rocketblaster/Devboard/attachments/3d_render.png

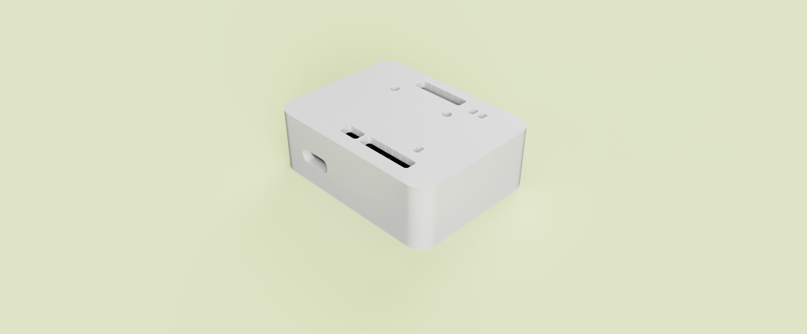
attachments/3d_render.png
