rocketblaster/Devboard/attachments/image3.png

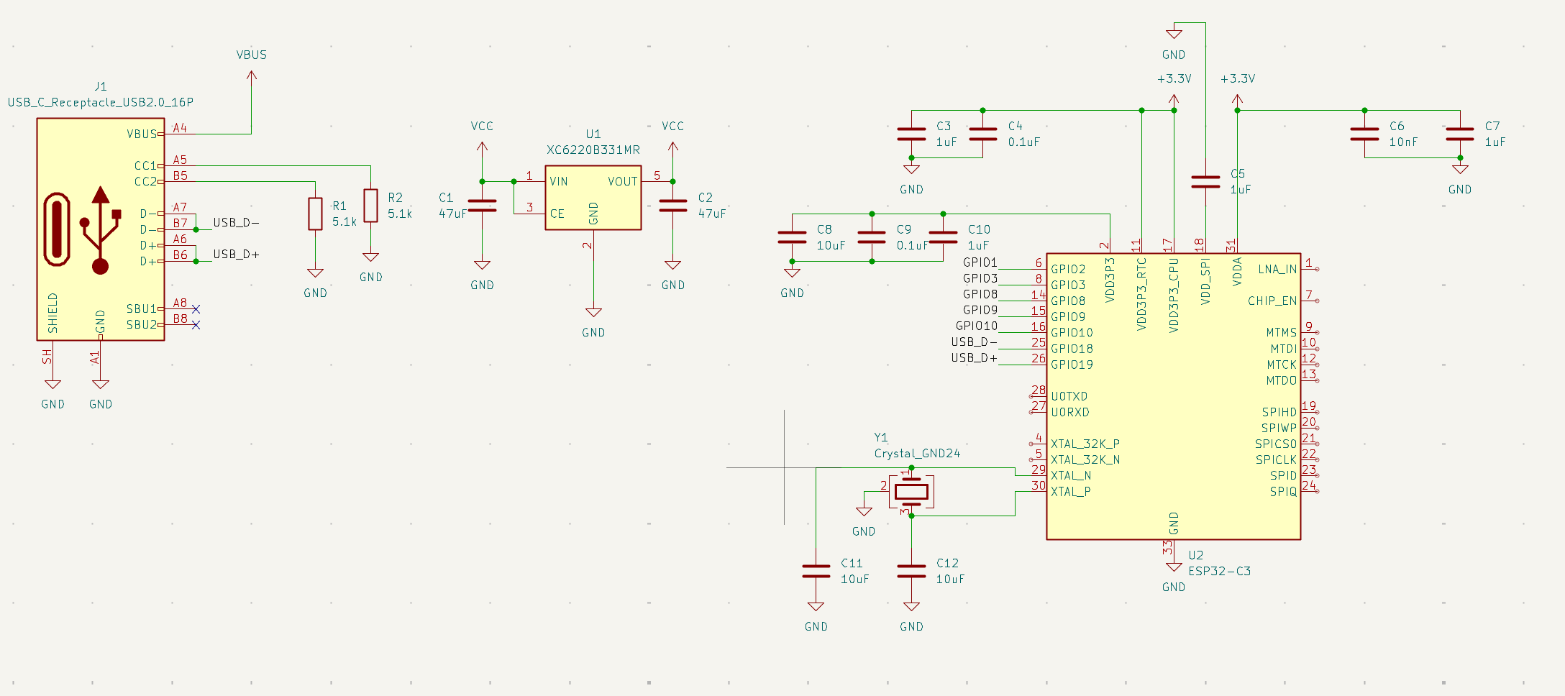
attachments/image3.png
