rocketblaster/Devboard/attachments/image12.png

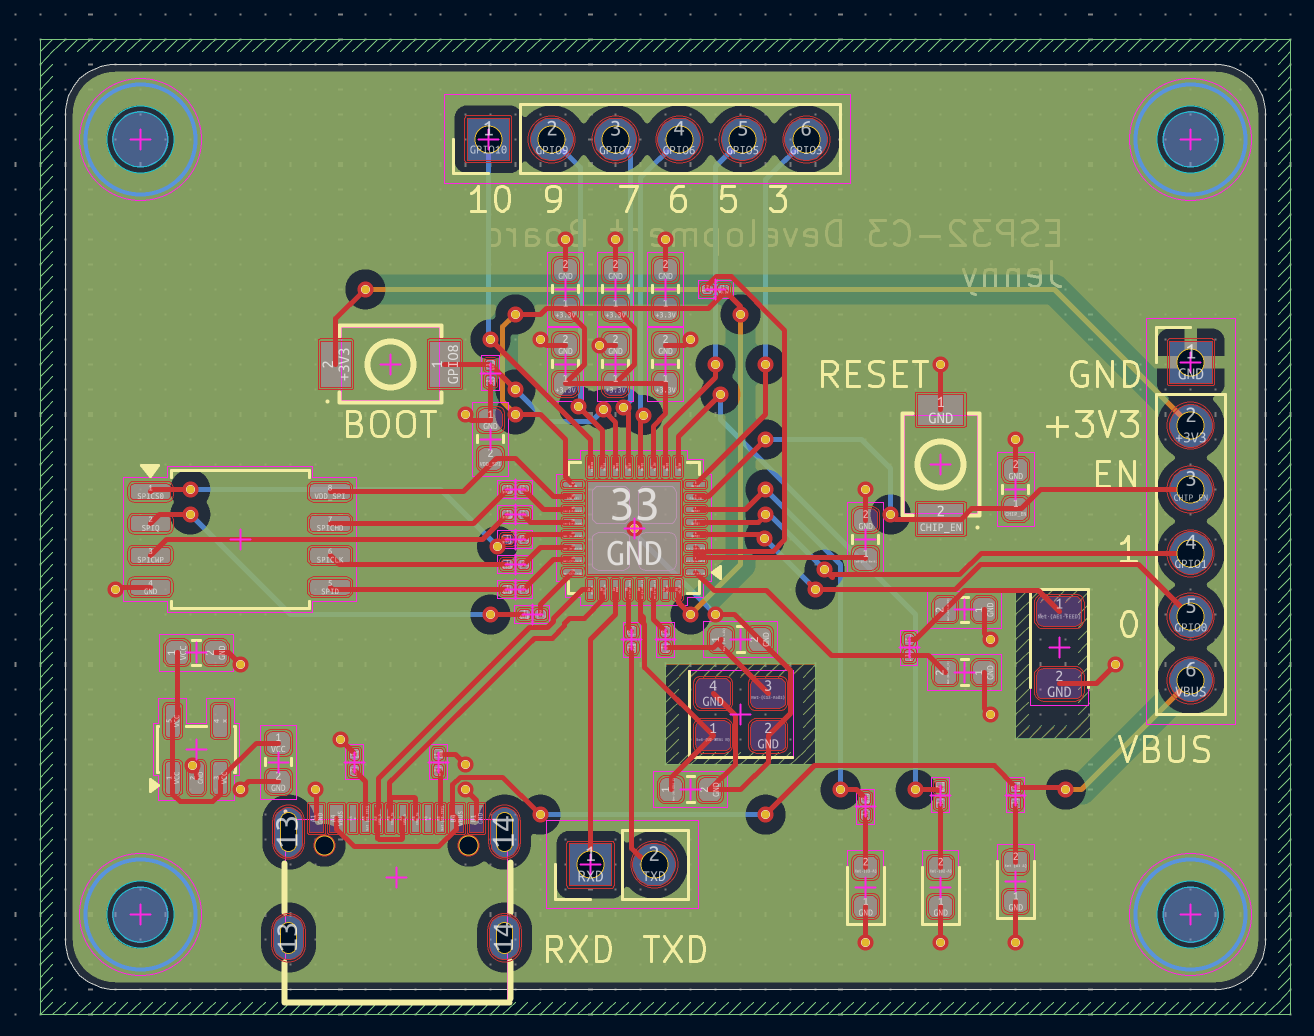
attachments/image12.png
