rocketblaster/Devboard/attachments/image15.png

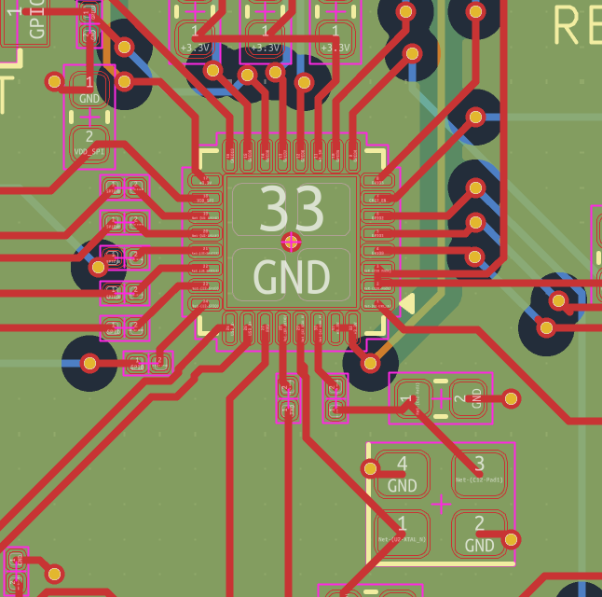
attachments/image15.png
