rocketblaster/Devboard/attachments/pcb-v2.png

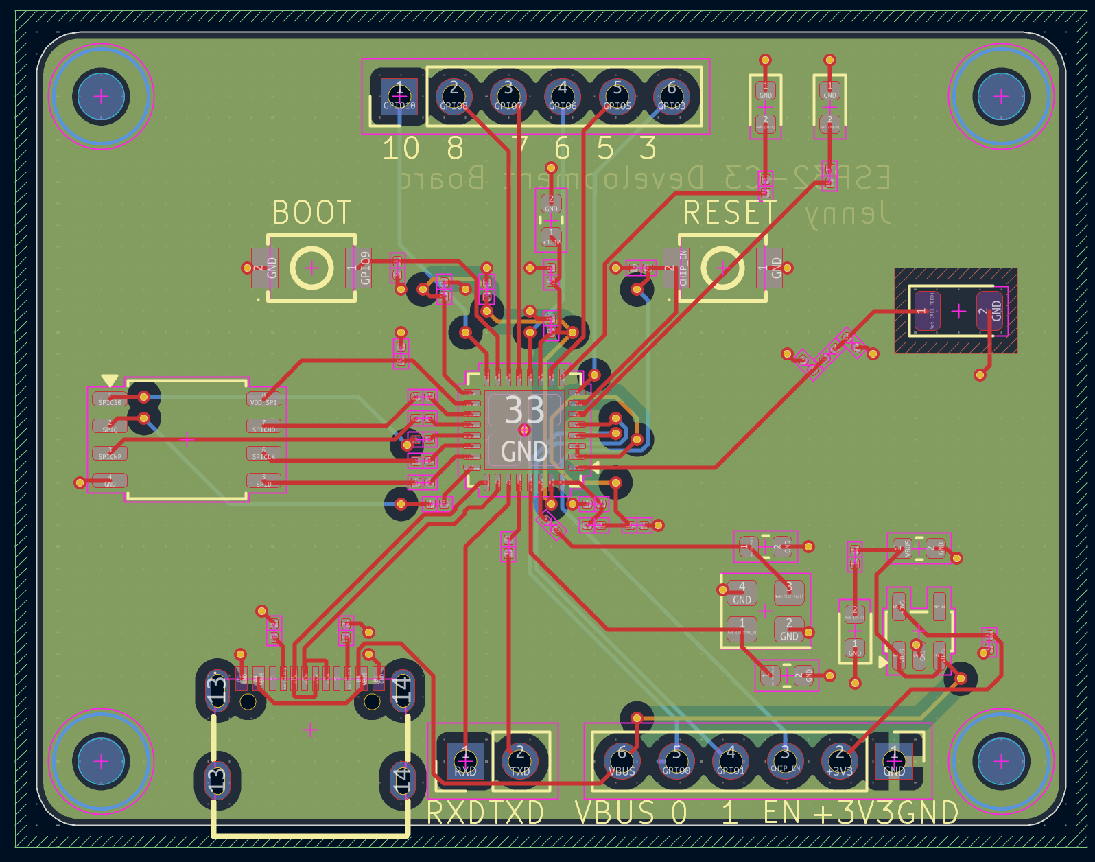
attachments/pcb-v2.png
