rocketblaster/Devboard/attachments/pcb-v3.png

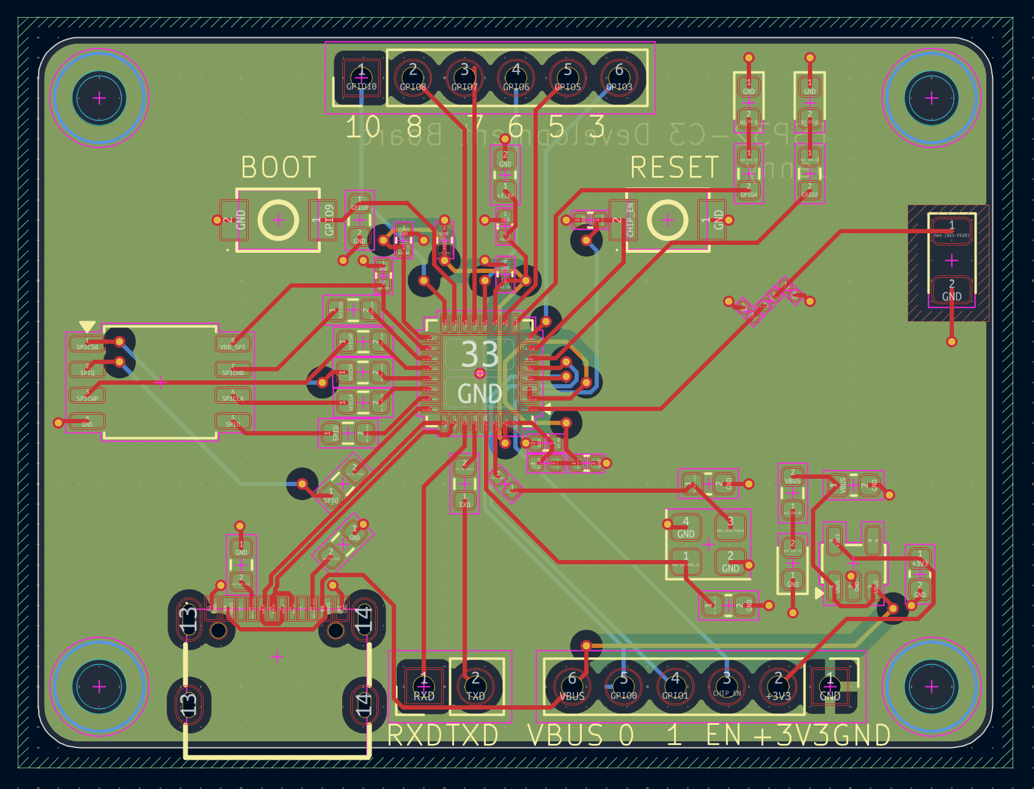
attachments/pcb-v3.png
