rocketblaster/Devboard/attachments/render-v1.png

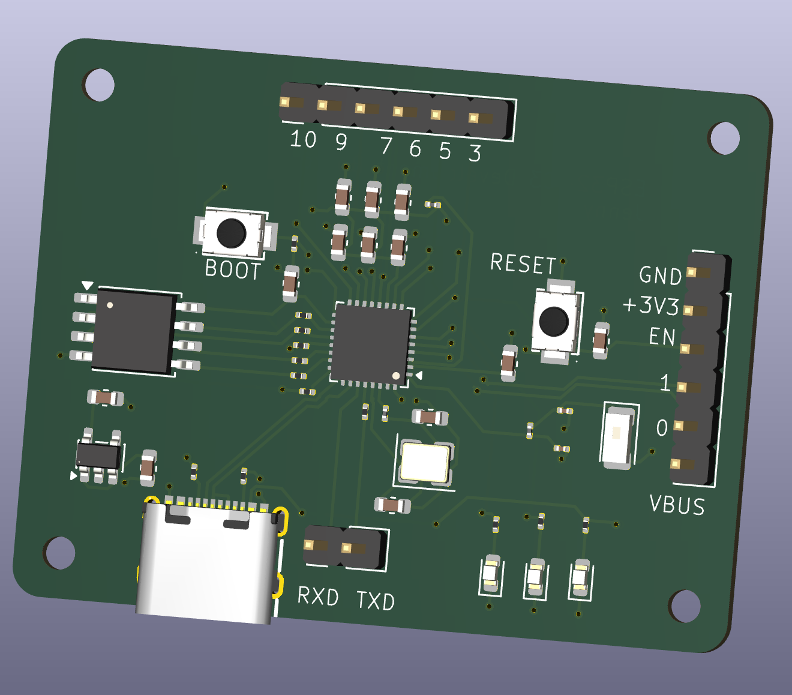
attachments/render-v1.png
