rocketblaster/Devboard/attachments/render-v2.png

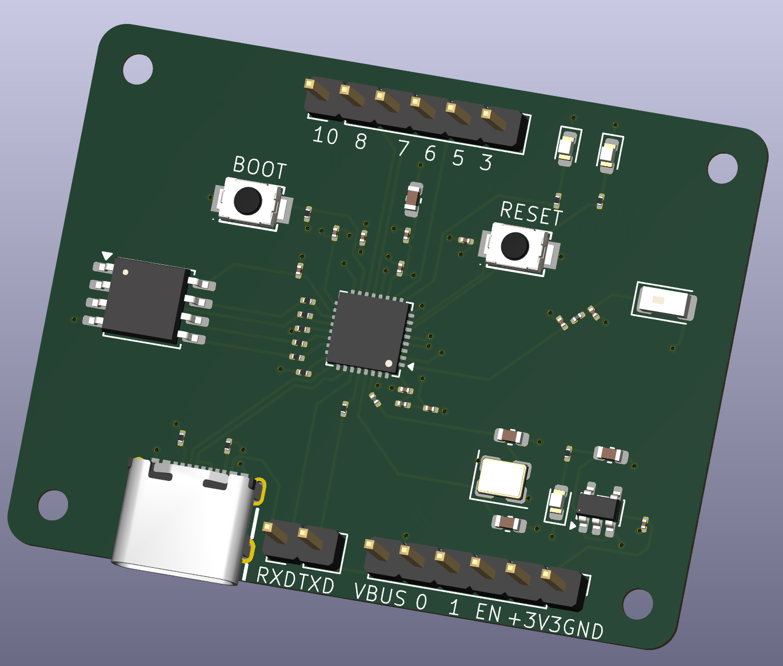
attachments/render-v2.png
